v0Ch/vfk-001/split hub compact 18.stl

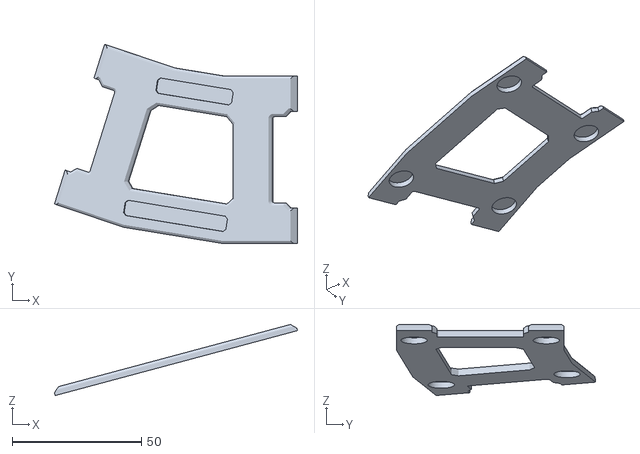
[picture p29: CAD file, 2023-02-10]
split hub compact 18.stl
94.0 x 77.0 x 27.5
