v0Ch/vfk-001/cluster sleve.stl

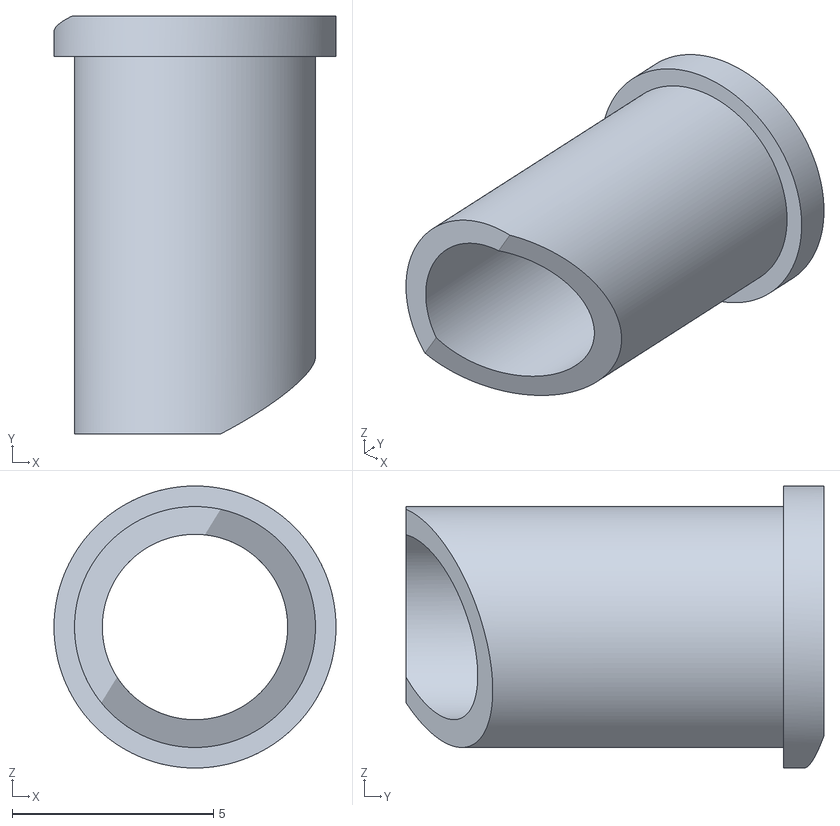
[picture p30: CAD file, 2023-02-10]
cluster sleve.stl
7.00 x 10.4 x 7.00
